audiyofan/Soco2/build/ltspice/version38P.asc

C1: cap; 100n
C2: cap; 100n
C3: cap; 220µ; V=250 Irms=1.23 Rser=0.34
C4: cap; 220µ; V=250 Irms=1.23 Rser=0.34
D2: zener; BZX84C6V2L
D3: diode
D4: diode
D5: diode
D6: diode
L1: ind2; 8.102759; Rser=36.7 Cpar=250p
L2: ind2; 0.05171889; Rser=0.5
L3: ind2; 8.102759; Rser=36.7 Cpar=250p
Q1: npn2; MJE340
Q2: npn2; MJE340
Q3: npn; MPSA42
Q4: npn; MPSA42
R1: res; 24k; tol=1 pwr=5
R2: res; 24k; tol=1 pwr=5
R3: res; 150
R4: res; 68k
R6: res; 90k
R7: res; 10k
R8: res; 47k
R9: res; 410; tol=1
R10: res; 220k
R11: res; 220k
R13: res; 150
R14: res; 68k
R17: res; 10Meg
R18: res; 8
U1: triode; 6S19P
U2: triode; 6S19P
U3: 6Z38PEXCEM
U4: 6Z38PEXCEM
U5: LM7905C
V1: voltage; SINE(0 0.7 1k); AC 1 1
V2: voltage; 350
V4: voltage; 97
V5: voltage; SINE(8.4 20m 100)
Named nets: 0, +HT1, -HT, CR, +HT2
.tran 5m
;ac oct 1000 10 200000
.measure OUTPUT_POWER_RMS RMS(V(CR))*I(R18)
.Fourrier 1000 V(CR)
K1 L1 L2 L3 0.99966656
