audiyofan/Soco2/build/power/6S19P.asc

R1: res; 470k
U1: triode2; 6S19P
VA1: voltage; 250
VA: voltage; 500
VG: voltage; 0
Named nets: 0, Ua
.dc Va 0 400 5 VG -0 -200 -20
