audiyofan/Soco2/built_version/ltspice/6Z38P_6S19P_push_pull_amplifier_ver_Tof_rev3.asc

C1: cap; 100n
C2: cap; 100n
C3: polcap; 220u; V=100 Irms=590m Rser=0.1 Lser=0 mfg="Nichicon" pn="UPR2A221MRH" type="Al electrolytic"
C4: polcap; 220u; V=100 Irms=590m Rser=0.1 Lser=0 mfg="Nichicon" pn="UPR2A221MRH" type="Al electrolytic"
C5: cap; 1u; V=100 Irms=4.58 Rser=0.025 Lser=0 mfg="KEMET" pn="C2225C105K1RAC" type="X7R"
D1: zener; BZX84C51L
D2: zener; BZX84C6V2L
D3: zener; BZX84C65L
D5: zener; BZX84C51L
D6: zener; BZX84C65L
J1: njf; 2N4392P
R1: res; 100K; tol=1 pwr=5
R2: res; 100K; tol=1 pwr=5
R3: res; 180
R4: res; 80k
R5: res; 220K; pwr=1
R6: res; 91k
R7: res; 1K
R8: res; 47k
R9: res; 300; tol=1
R10: res; 220k
R11: res; 220k
R12: res; 100K; pwr=1
R13: res; 180
R14: res; 80k
R15: res; 10
R16: res; 10
R17: res; 470
R18: res; 8
R19: res; 470
R21: res; 1K
R22: res; 1K
R23: res; 100K; tol=1 pwr=5
R24: res; 100K; tol=1 pwr=5
R25: res; 100K; tol=1 pwr=5
R26: res; 100K; tol=1 pwr=5
U1: 6S19P
U2: 6S19P
U3: 6Z38PEXCEM
U4: 6Z38PEXCEM
U5: TRSDA6S19P
U6: MJE340
U7: MJE340
V1: voltage; SINE(0 1.5 1k); AC 1 1
V2: voltage; 372
V5: voltage; SINE(10 20m 100)
Named nets: 0, +HT1, -HT, CR
;ac oct 1000 10 200000
.Fourrier 1000 V(CR)
.tran 5m
.measure POWER_VCR AVG(V(CR))**2 /8 from 0m to 5m
