audiyofan/Soco2/built_version/ltspice/alim_Tof_rev2.asc

C1: polcap; 220u; V=100 Irms=590m Rser=0.1 Lser=0 Rpar=2Meg mfg="Nichicon" pn="UPR2A221MRH" type="Al electrolytic"
C2: polcap; 100u; V=100 Irms=385m Rser=0.18 Lser=0 Rpar=2Meg mfg="Nichicon" pn="UPR2A101MRH" type="Al electrolytic"
C3: polcap; 470u; V=50 Irms=1.47 Rser=0.07 Lser=0 Rpar=2Meg mfg="Panasonic" pn="ECA1HFQ471S" type="Al electrolytic"
C4: polcap; 100u; V=100 Irms=385m Rser=0.18 Lser=0 Rpar=2Meg mfg="Nichicon" pn="UPR2A101MRH" type="Al electrolytic"
C5: polcap; 100u; V=100 Irms=385m Rser=0.18 Lser=0 Rpar=2Meg mfg="Nichicon" pn="UPR2A101MRH" type="Al electrolytic"
C6: polcap; 22u; V=63 Irms=240m Rser=1 Lser=0 Rpar=2Meg mfg="Panasonic" pn="ECA1JFQ220" type="Al electrolytic"
D1: diode; UF4007
D2: diode; UF4007
D3: diode; UF4007
D4: diode; UF4007
D5: diode; UF4007
D6: diode; UF4007
D7: LED; LEDVERTE
D8: zener; BZX84C12L
D9: diode; UF4007
D10: diode; UF4007
I1: current; 70m
I2: current; 70m
I3: current; 20m
R1: res; 180
R5: res; 1k
R6: res; 390
R8: res; 180
R9: res; 47
V1: voltage; SINE(0 401 50); AC 1 0
V2: voltage; SINE(0 24 50); Rser=1
Named nets: -HT, HT1, HT2L, HT2R, 0
.tran 0 40s 15m
